ELAScience/AQ-drone/images/IMG_7116.jpeg

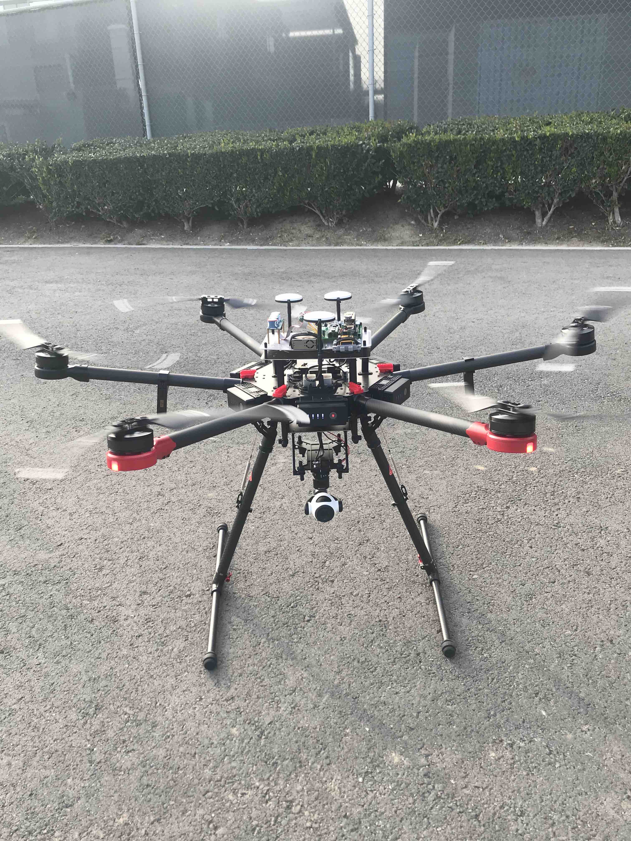
images/IMG_7116.jpeg
