ELAScience/AQ-drone/images/IMG_7122.jpeg

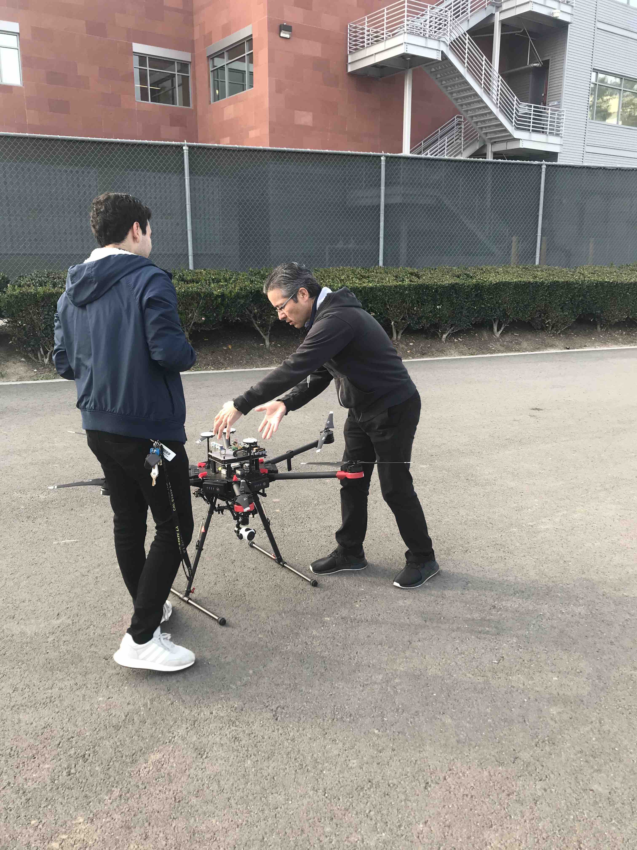
images/IMG_7122.jpeg
