ELAScience/AQ-drone/images/IMG_7123.jpeg

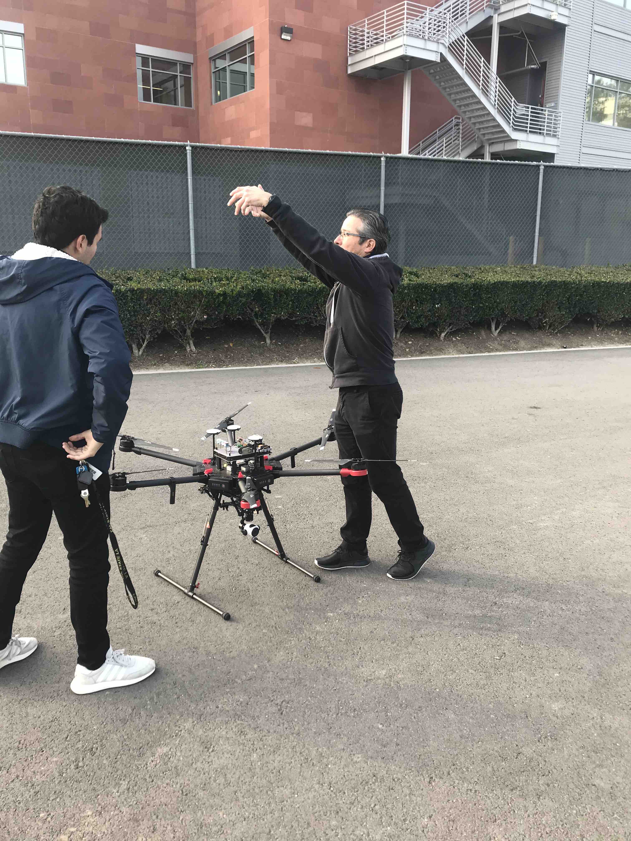
images/IMG_7123.jpeg
